HuaqiuOpenHardware/xinghongpai-nearlink-dev-board/firmware/examples/202_heart_rate/bsp_max30102_blood.h

#ifndef __BSP_MAX30102_BLOOD_H__
#define __BSP_MAX30102_BLOOD_H__

void max30102_fir_init(void);
void ir_max30102_fir(float *input,float *output);
void red_max30102_fir(float *input,float *output);

#endif
